Technology-for-the-Poorest-Billion/2026-Ideabatic/interim/Ideabatic 2nd presentation.pdf

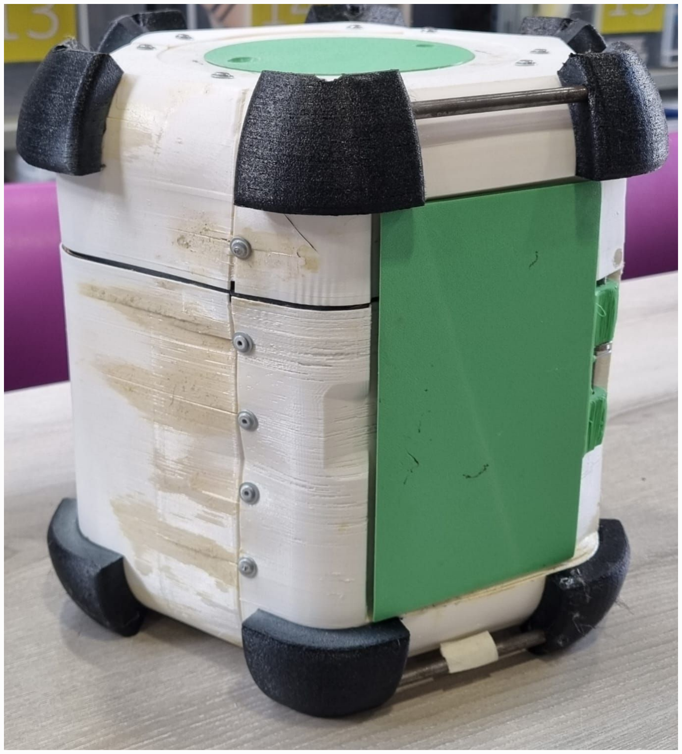
[picture p62: figure]

# IDEABATIC

# SMILE GO Project

# Uniform Cooling Solutions

### Interim Presentation by Karen, Kerry, and Kavita

# Proposal Recap

SMILE GO - Investigating the causes of Asymmetric Cooling & potential ways to reduce it

- In thermal tests the SMILE coolers have shown significant temp difference between top and bottom vaccine carousel chambers
- Issue because vaccines must be stored in small range (2-8°C)
- Design & test cooler inserts
- Investigate impact of convection
- Investigate any other potential causes
- Consider new designs based on our findings

What we will do:

18/05 - 1/06

# Progress So Far

01

# Electronics

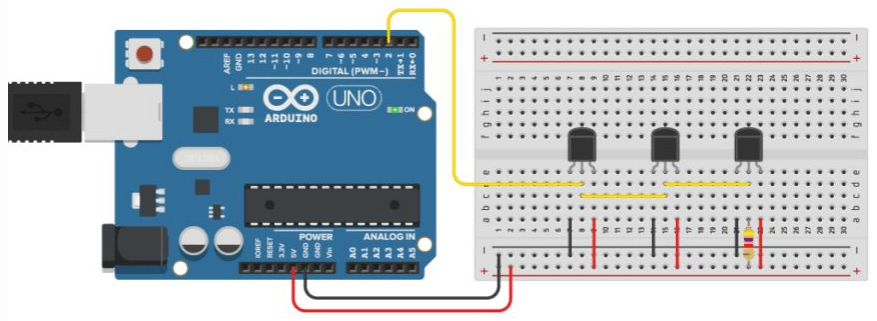
[picture p63: figure]

Supplies | Quantity | Source
DS18B20 | x5 (6) | RS components
breadboard | x1 | CUED
Arduino Uno | x1 | CUED
SD card module | x1 | CUED
4.7k resistor | x1 | CUED
RTC | x1 | RS components

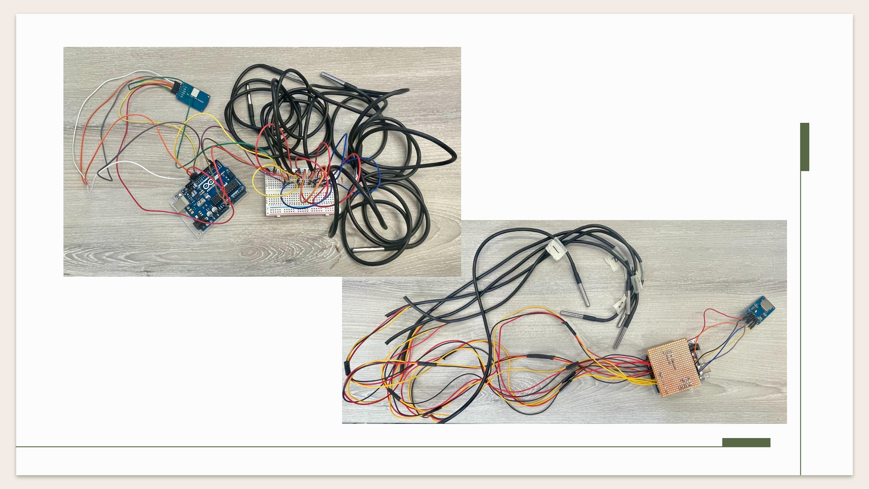
[picture p64: page 5]

# Insert Designs

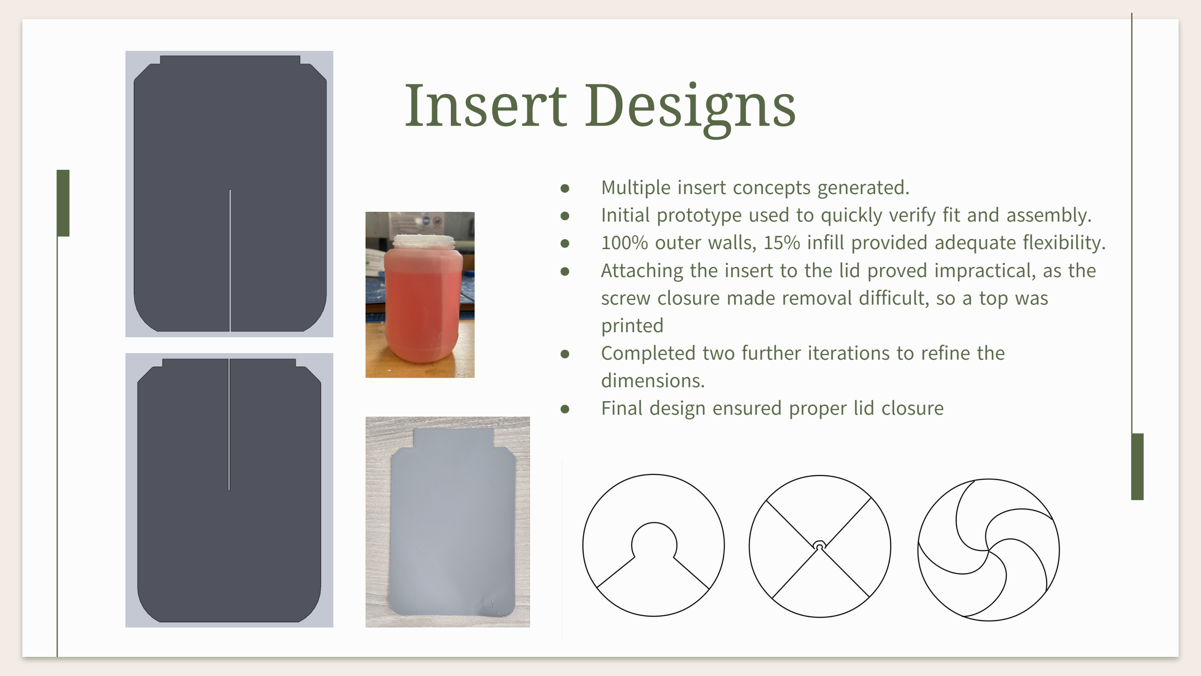
[picture p65: page 6]

- Multiple insert concepts generated.
- Initial prototype used to quickly verify fit and assembly.
- 100% outer walls, 15% infill provided adequate flexibility.
- Attaching the insert to the lid proved impractical, as the screw closure made removal difficult, so a top was printed
- Completed two further iterations to refine the dimensions.
- Final design ensured proper lid closure

# Waterproofing and Freezing

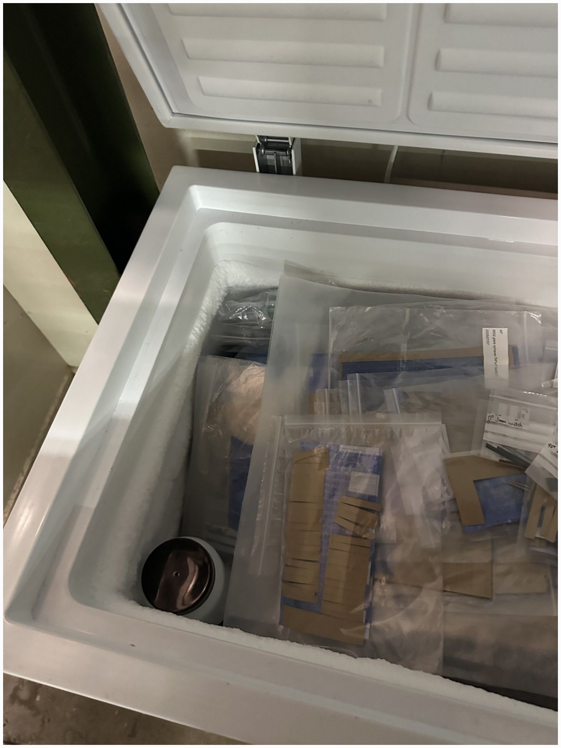
[picture p66: figure]
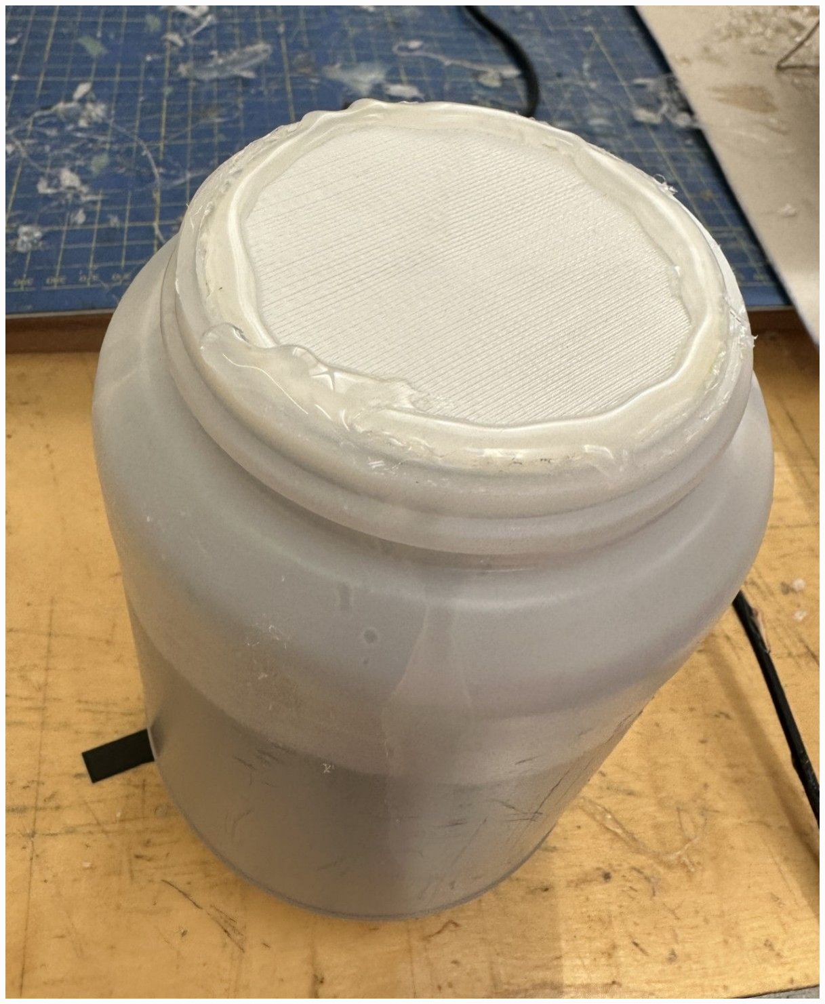
[picture p67: figure]

Hot glue was used to bond the insert into the bottle and form an airtight/watertight seal.

3D print did show some wicking between the extrusion lines using the RS Ideawork printers

The bambu printed lid remained dry

Frozen in the materials lab

# Hot Gluing

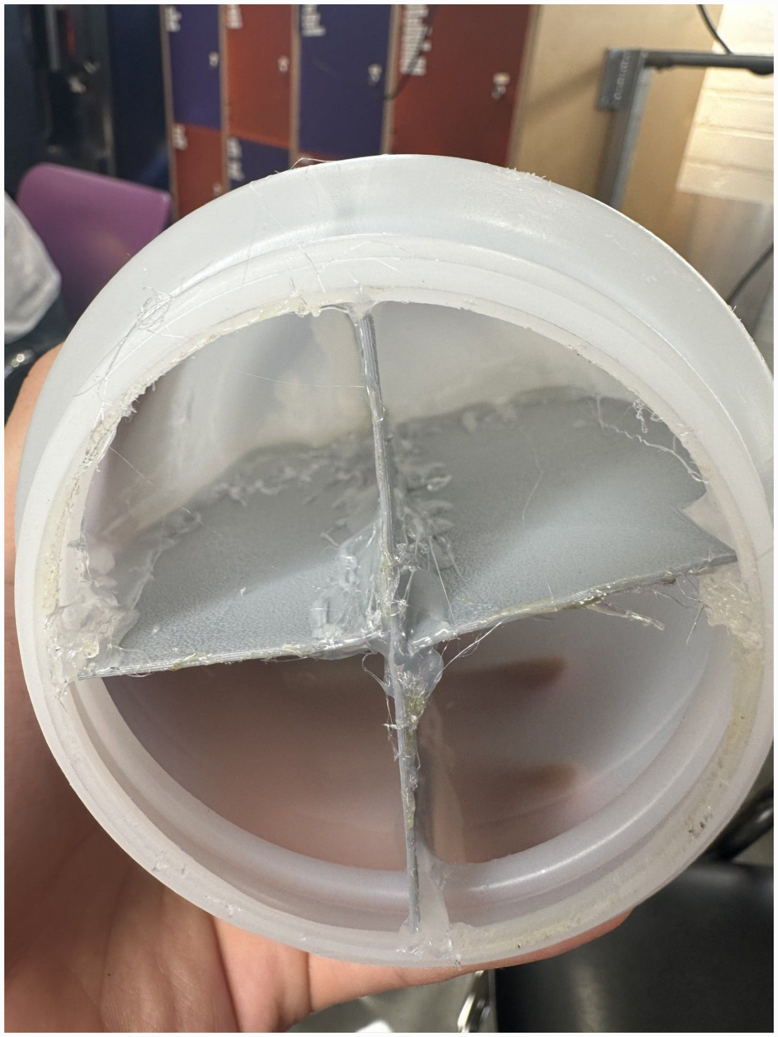
[picture p68: figure]

Extremely sticky. Practice gluing was performed on a sample that was not used for a test to learn more about the process.

The best method seemed to be letting gravity pull the glue down into the interfaces, rather than using sticks or tools to guide the glue.

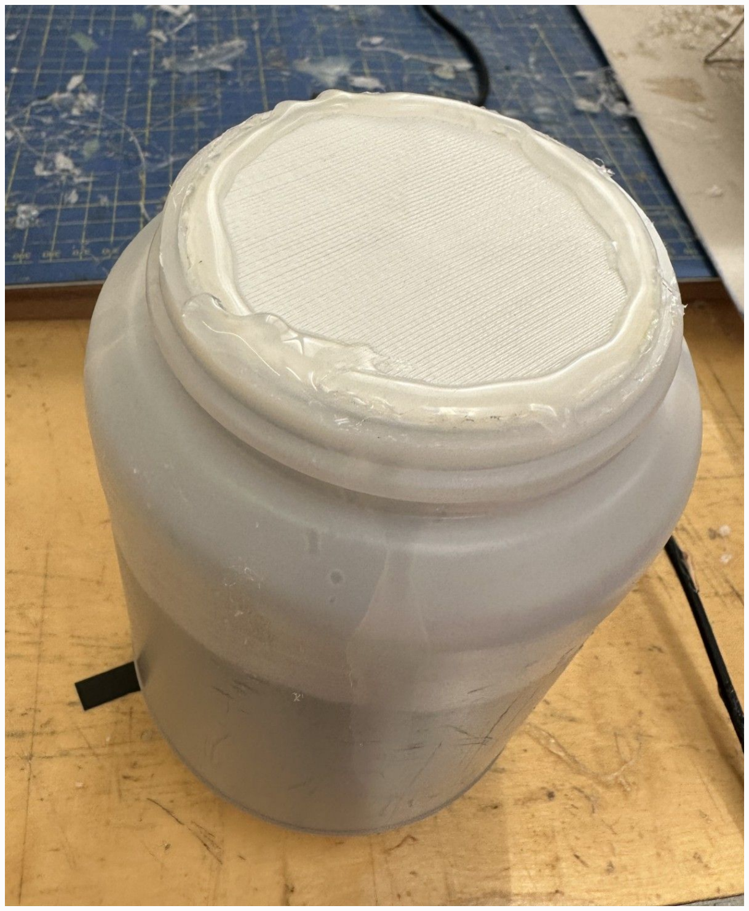
[picture p69: figure]

Further issues include navigating the threaded section of the bottleneck, and gluing the final cap on the bottle.

No “touch-ups” can be made to the lid seal after it is on. This is a very important step in the sealing process.

Water must be added prior to lid gluing.

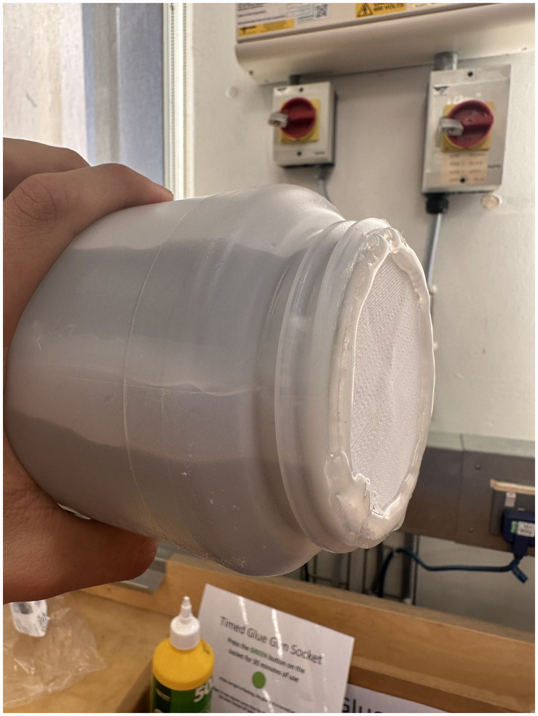
[picture p70: figure]

The seal is airtight and watertight.

Several intermittent testing stages were performed during the gluing process - check and re-apply glue to leaking spots.

A freeze-thaw cycle was performed before testing - the structural integrity of the inserts and seal remained sound.

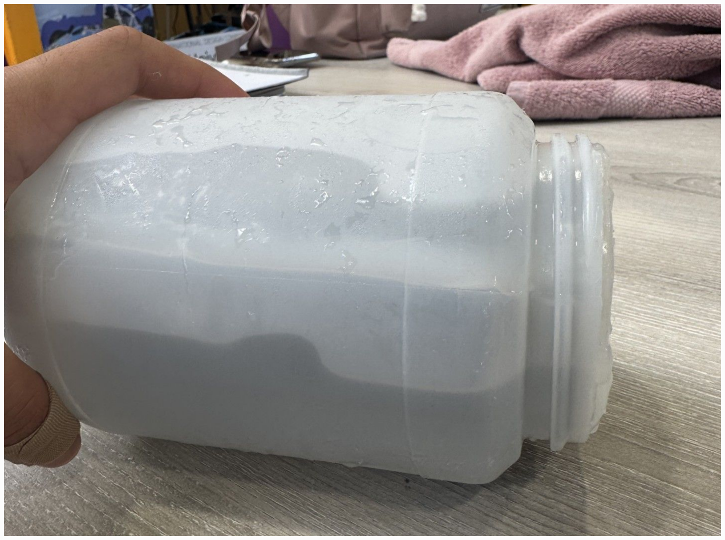
[picture p71: figure]

Updates Hot Glue Expenditure: ~£5

# Gluing Effectiveness

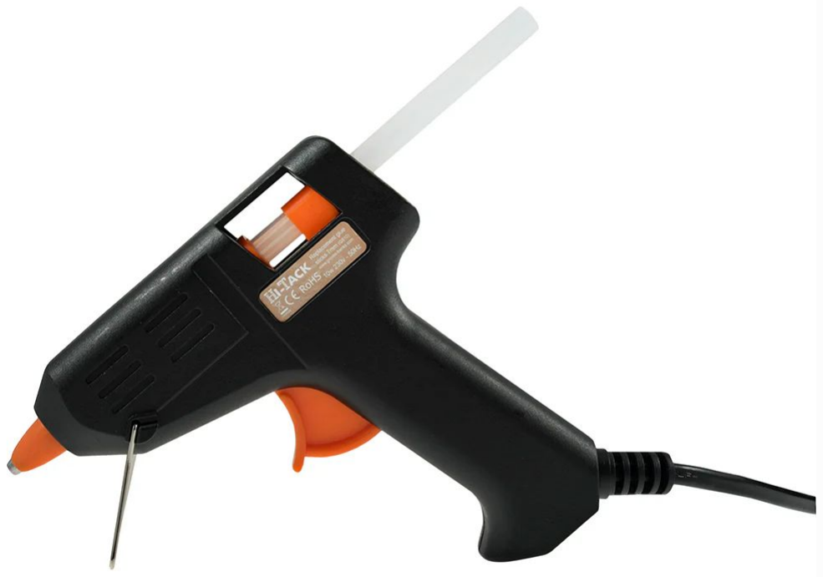
[picture p72: figure]

Removal of the insert and hot glue seal in the bottle can be done with minimal damage to the bottle.

A check was performed prior to insert addition to assess hot glue adhesion properties to the bottle.

Hot glue delaminates from the HDPE bottle with enough force.

Inserts are damaged in the process, so once they are removed, they cannot be reused.

# Hot Glue and Insert Removal

- Prototype Material Selection
- PLA chosen for rapid, low-cost manufacture
- Hot glue used to create temporary airtight seals for testing.
- Key Issues Identified
- Water permeation through the printed structure due to print porosity.
- PLA experiences hydrolytic degradation over time
- Potential degradation of PLA and adhesive seals during freeze-thaw cycling.
- Design Improvements
- Higher-quality Bambu printing reduced porosity and improved consistency.

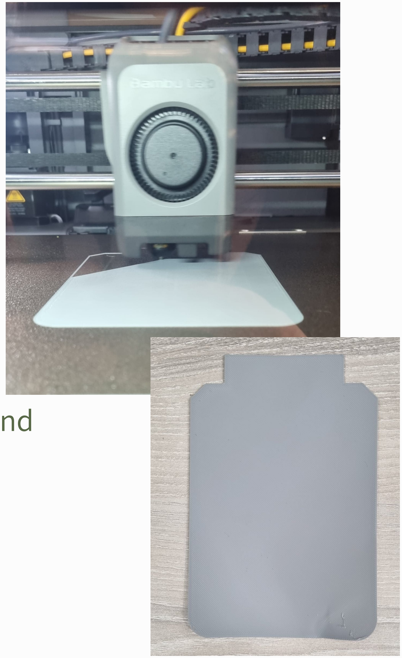
[picture p73: figure]

- PETG identified as a more suitable material due to improved water resistance and takes up less moisture
- Future Manufacturing
- Current solution suitable for prototyping only.
- Integrated blow-moulded chambers.
- Silicon sealant remains flexible, epoxy coating

# Material Research for Insert Design

# Experimental set-up

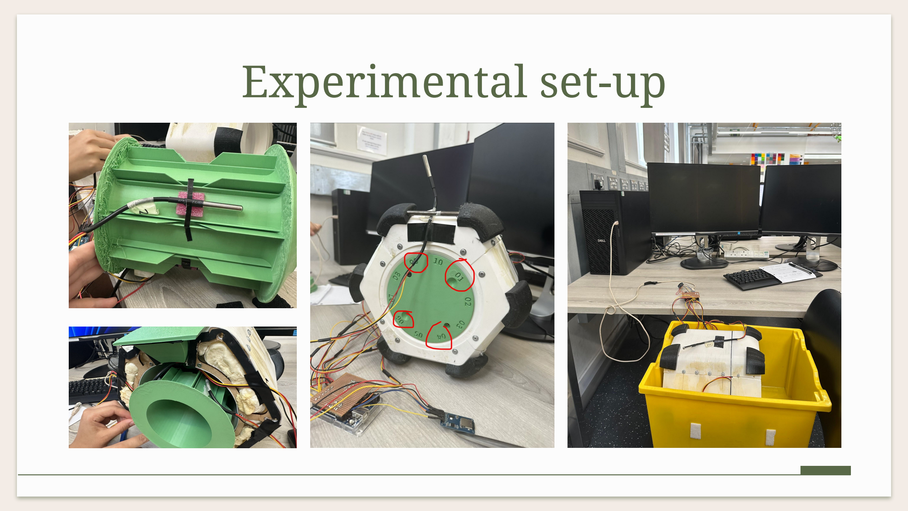
[picture p74: page 12]

01 Control test - 24 hour control test with the current set-up and the door on top (no inserts).

# Experimental testing

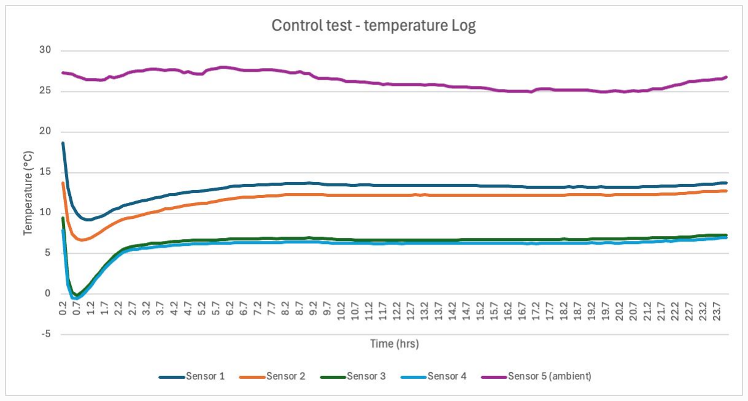
[picture p75: figure]

Results: Initial difference in temperature (1st measurement 5mins in). Temperature drops significantly then rises back to a stable temperature after 5-6 hours

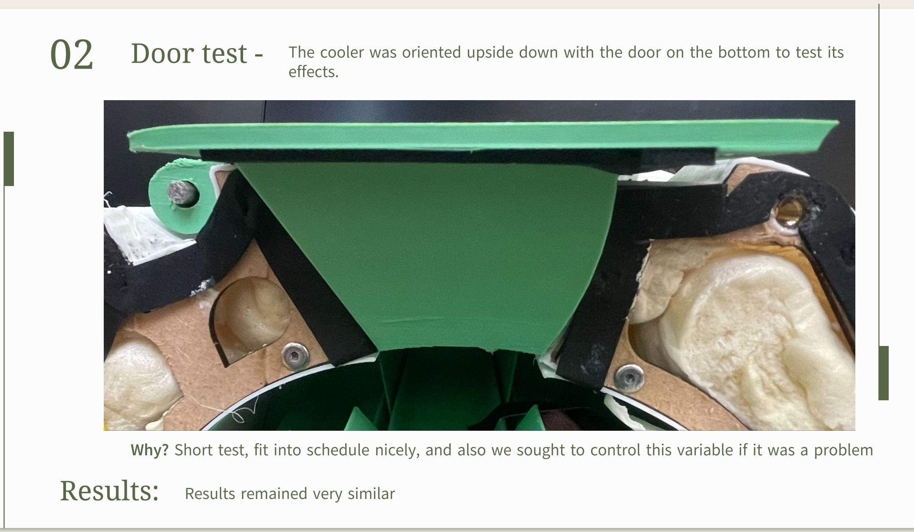
[picture p76: figure]
Door test -; Results:; Results remained very similar; effects.

Why? Short test, fit into schedule nicely, and also we sought to control this variable if it was a problem

The cooler was oriented upside down with the door on the bottom to test its

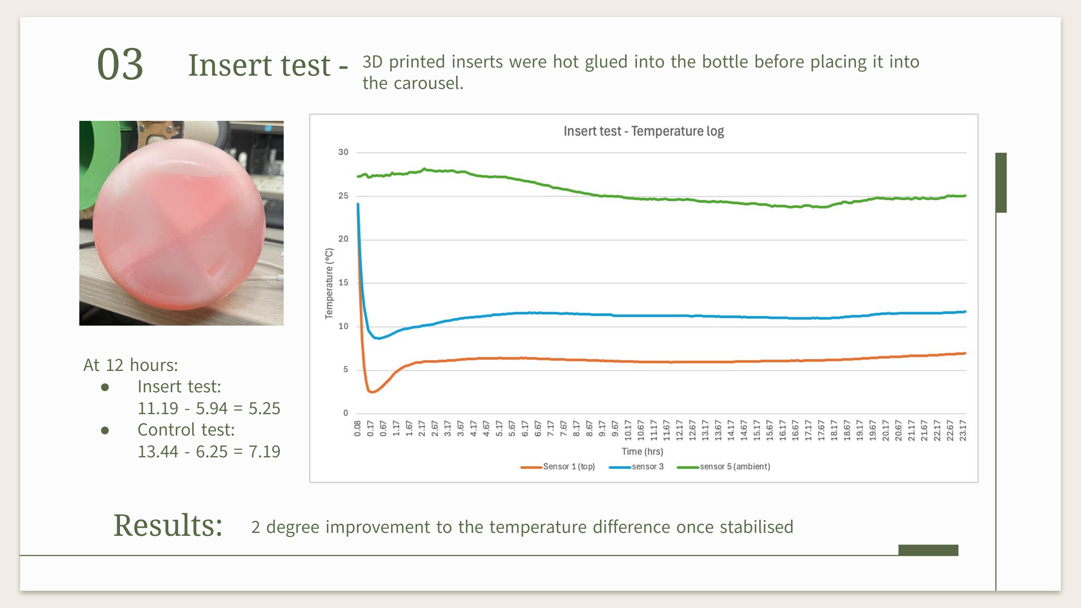
[picture p77: page 15]

03 | 3D printed inserts were hot glued into the bottle before placing it into
the carousel. Insert test -

Results: 2 degree improvement to the temperature difference once stabilised

At 12 hours:
- Insert test:
11.19 - 5.94 = 5.25
- Control test:
13.44 - 6.25 = 7.19

04

## Top thermal contact test -

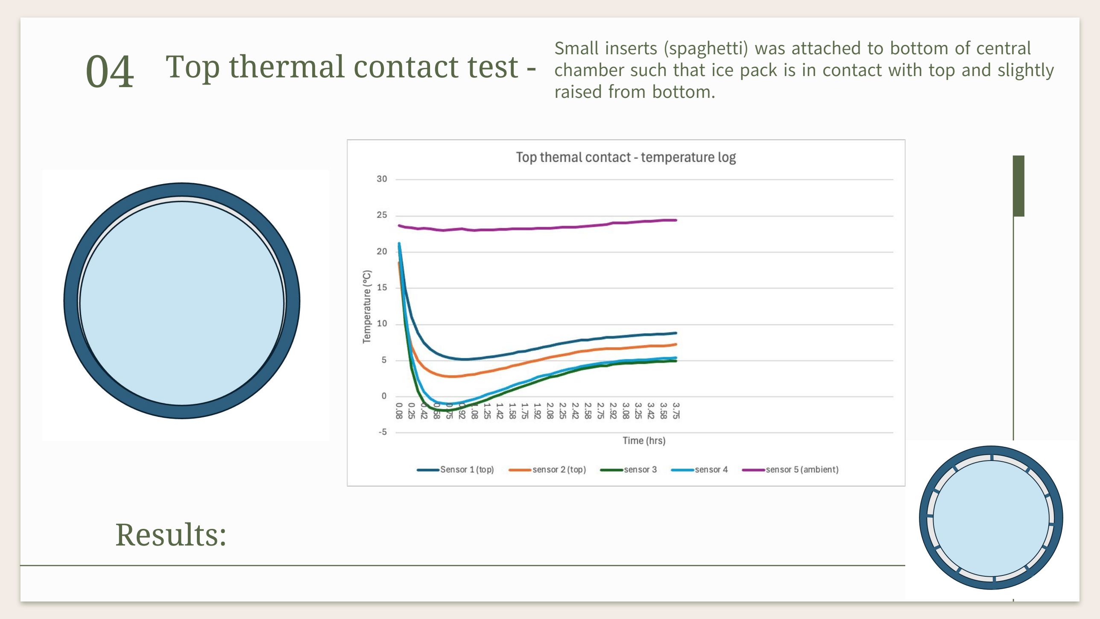
[picture p78: page 16]

Small inserts (spaghetti) was attached to bottom of central chamber such that ice pack is in contact with top and slightly raised from bottom.

## Results:

# Convection Research

- Research into convection-based experimental methods and setup designs
- Convection Resistance Design - radial planes in vaccine carousel
- Forced Convection - fan-induced convection and mixing

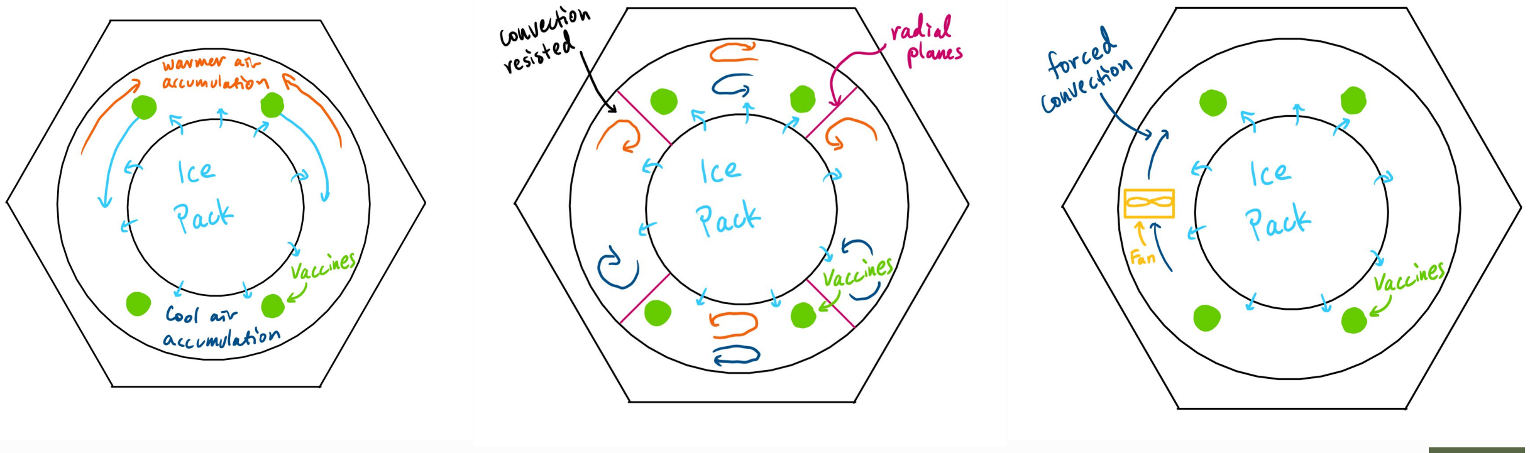
[picture p79: figure]

# Convection Prototype

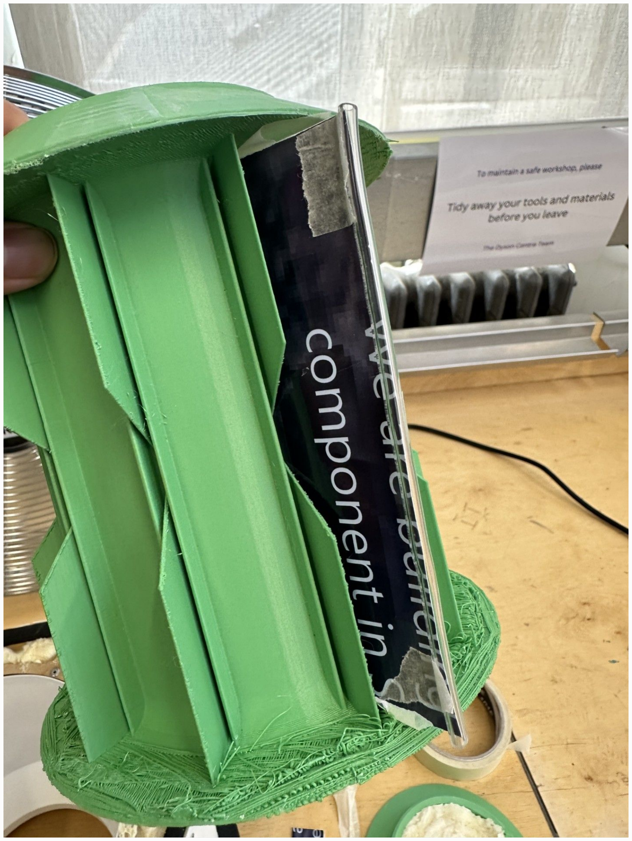
[picture p80: figure]
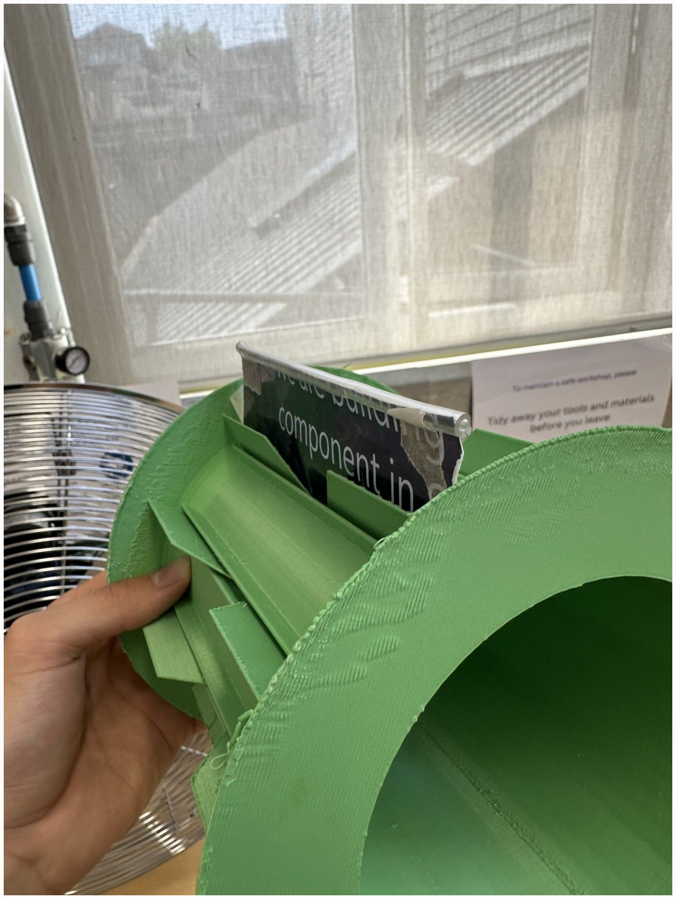
[picture p81: figure]

A brief model of the experimental setup for the convection resisting design was constructed.

- Assessment of how difficult it may be to get a decent seal within the vaccine chamber.
- Conclusion: very difficult, especially with assembly considerations.

However, it is still worth performing the test to assess the effectiveness of a simple carousel design which may end up mitigating the non-uniform cooling issue.

We want to see, if convection is the issue, if a simple redesign of the carousel can effectively even out the cooling.

# Documentation

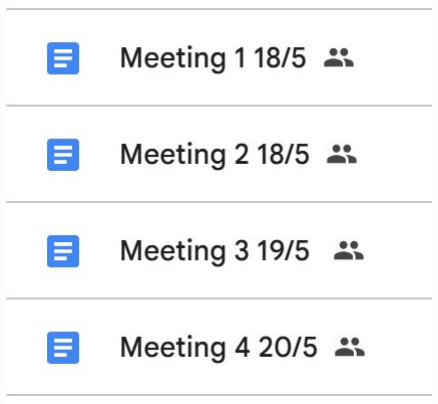
[picture p82: figure]

- Document of images taken throughout the project -important to keep track of specific design choices and for use in presentations or report.
- Meeting summaries consistently taken to keep track of ideas and possible changes to the project.

# Further Issues

02

Issue Encountered | Mitigation
Delays in sensor procurement affected the original testing schedule | Adapted the schedule and prioritised alternative tasks
Only one cooler bottle was available for testing and the current bottle is sold out | Carefully planned testing schedules to maximise bottle usage
Communication over text messages was sometimes ineffective in conveying ideas | Consistent and increased the frequency of in-person meetings
Early-stage challenges with file organisation and access across the team | Adopted Google Drive for centralised file sharing
Uncertain if the test will fail overnight or the computer has to be turned off | SD card stores any data till that point. We have contingency plans in case we can’t access the computer

# Personal and Technical development

03

# Kerry

- Attention to detail - The hot gluing process requires patience and a willingness to redo sections to get a sufficient seal.
- Importance of iteration and practice
- Communication with technicians and experts

# Kavita

- Code and arduino debugging (COM port issues)
- Soldering skills
- Time management & adaptability

# Karen

- Learning practical constraints of 3D printing (porosity, print settings, material selection)
- Iterative designing
- Time management

# Project timeline development

04

# Updated Gantt Chart

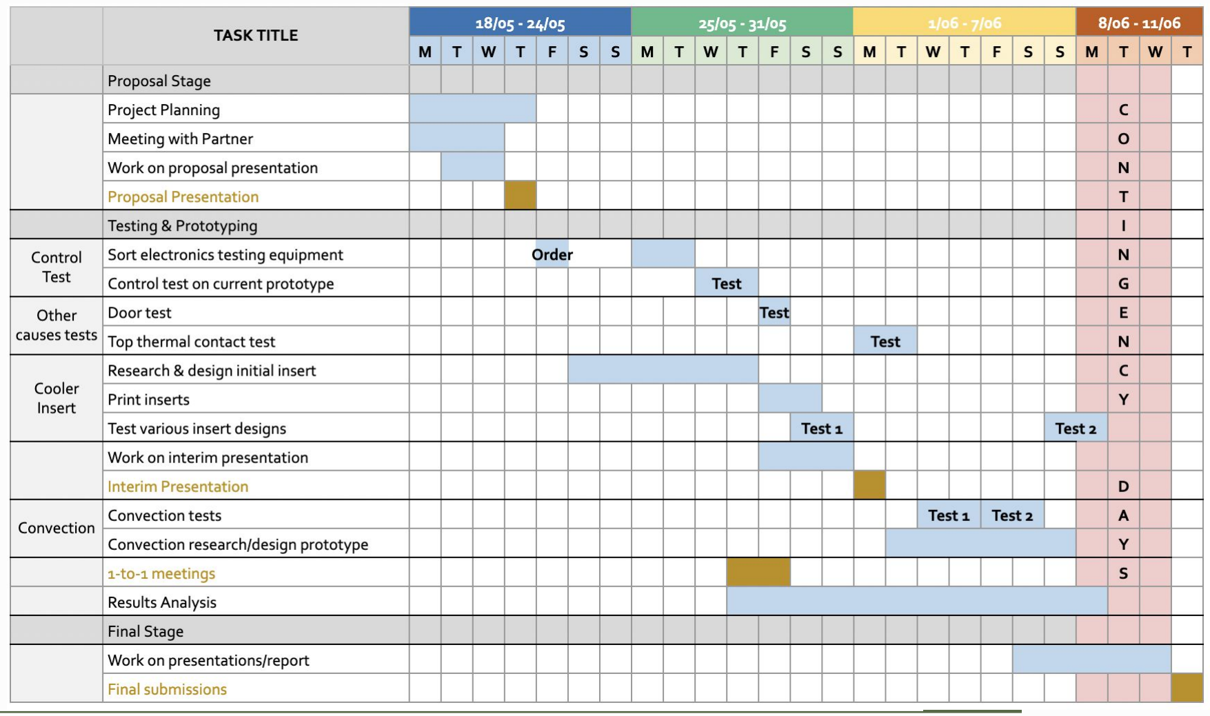
[picture p83: figure]

### Further Testing

# Future plans

- Convection test - fan (contacted Kevin for purchasing), radial planes.
- Investigate effect of contact of the ice pack with only the lower section of the carousel on non-uniform cooling.

### Analyse Results

- Compile the test data to analyse any significant changes.

### Design Changes

- Provide possible solutions to any identified causes of non-uniform cooling.

### Key Findings

- There is a large initial temperature difference occurs during the first 10 minutes.
- Door leakage largely ruled out
- Ice segmentation showed some promise of improving cooling uniformity.
- No definitive root cause identified. Further investigation required.
- Better Insulation required in the SMILE Go to keep vaccines in correct range

# Thank you for listening

### Any questions?
