Technology-for-the-Poorest-Billion/2026-Ideabatic/final/Technical Files/Research and Documentation/Image Documentation/Documentation_Images.pdf

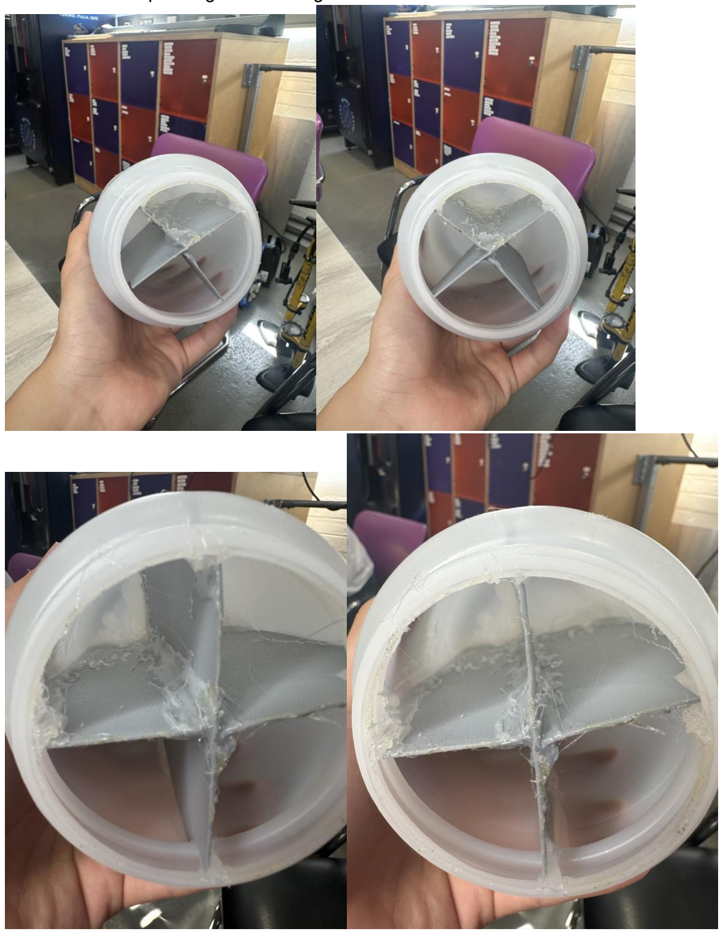
[picture p104: figure]

First insert water proofing and freezing:

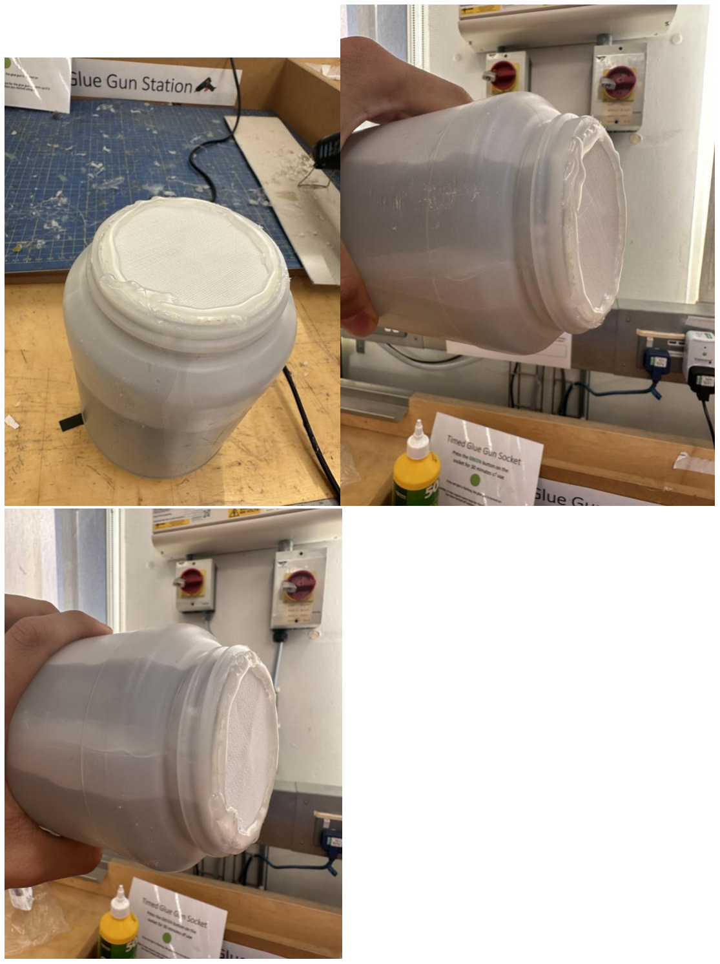
[picture p105: figure]

Once frozen and thawed to a large degree:

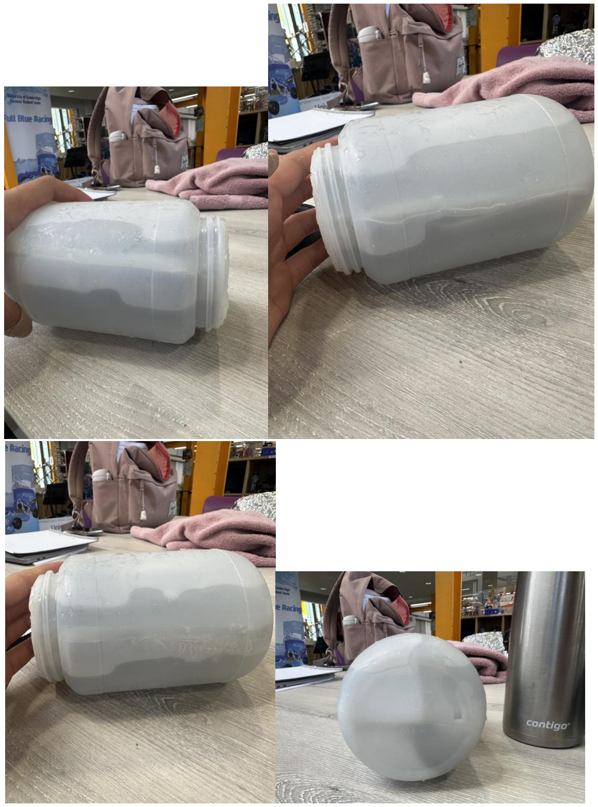
[picture p106: figure]

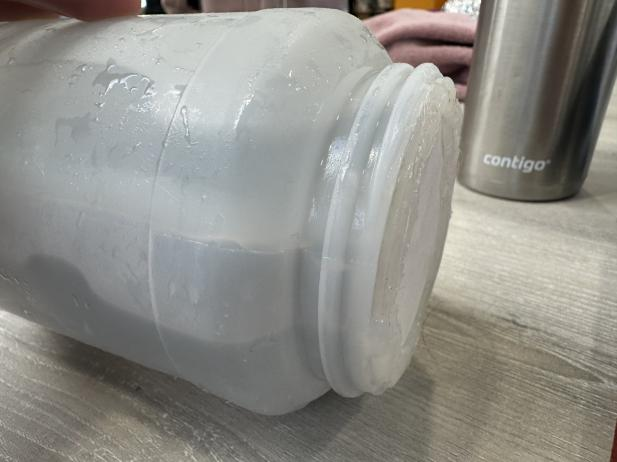
[picture p107: figure]

3D print of the insert initially:

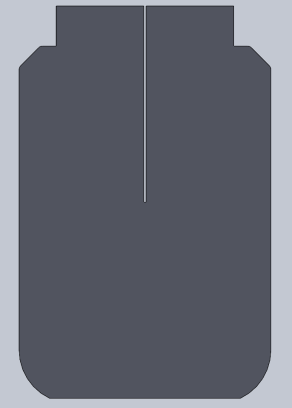
[picture p108: figure]
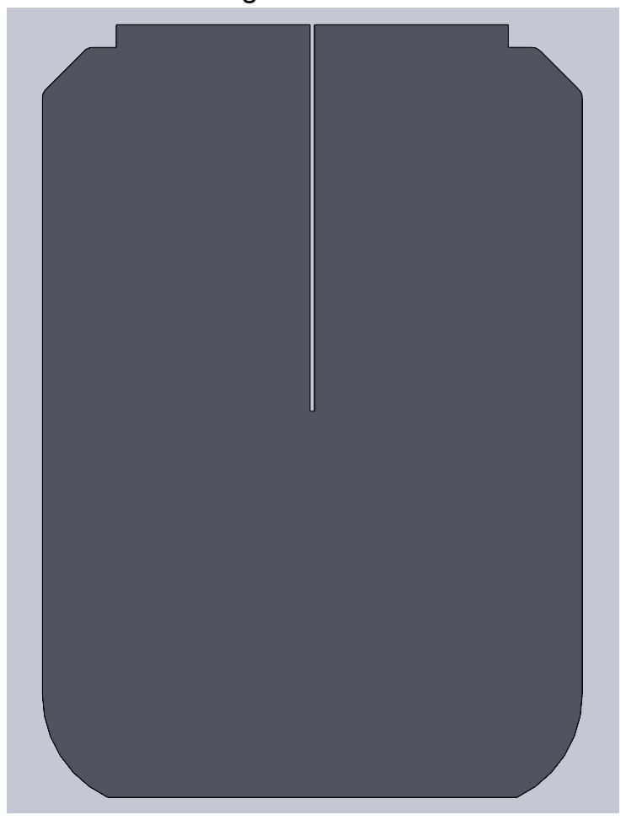
[picture p109: figure]

Newer insert design:

Convection FIrst test with tape and rubber seal:

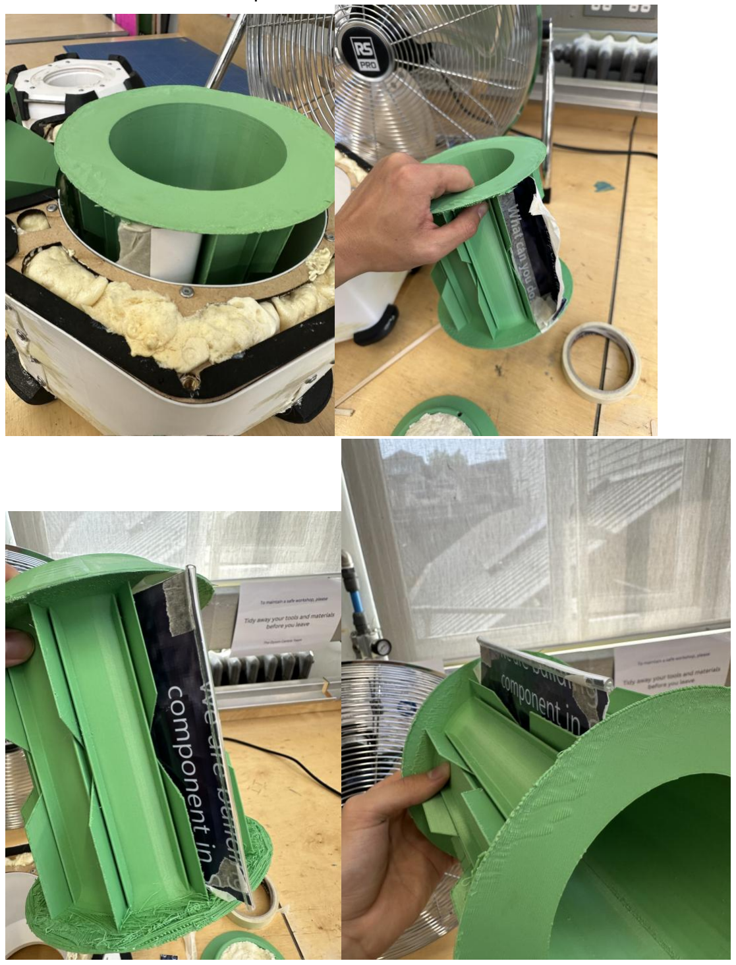
[picture p110: figure]

Freezer in the Materials Lab:

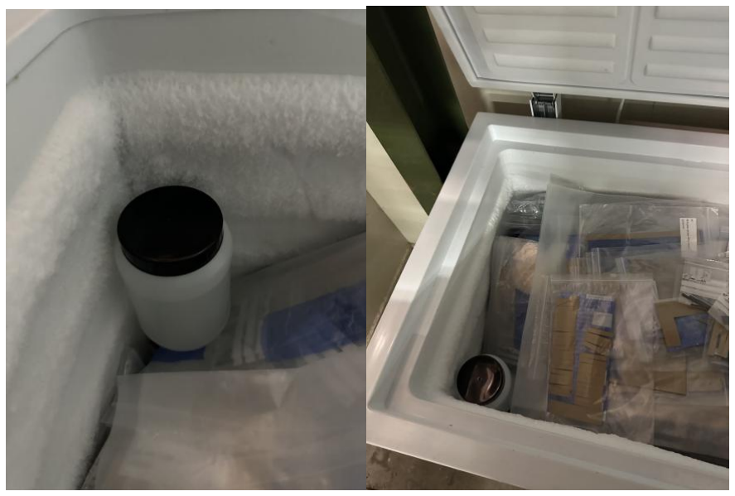
[picture p111: figure]

Frozen control:

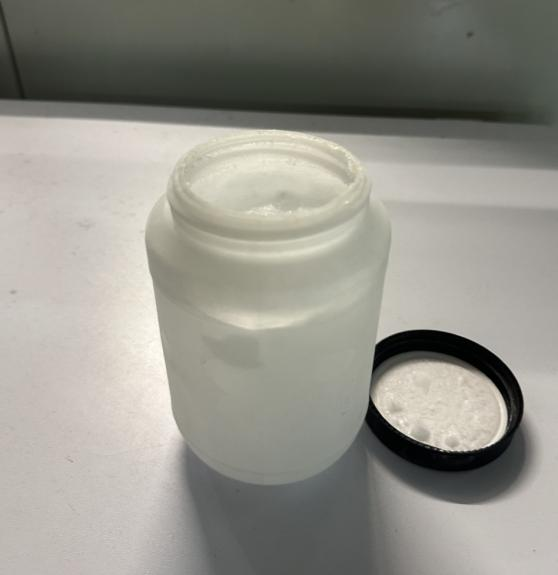
[picture p112: figure]

Initial breadboarded circuit:

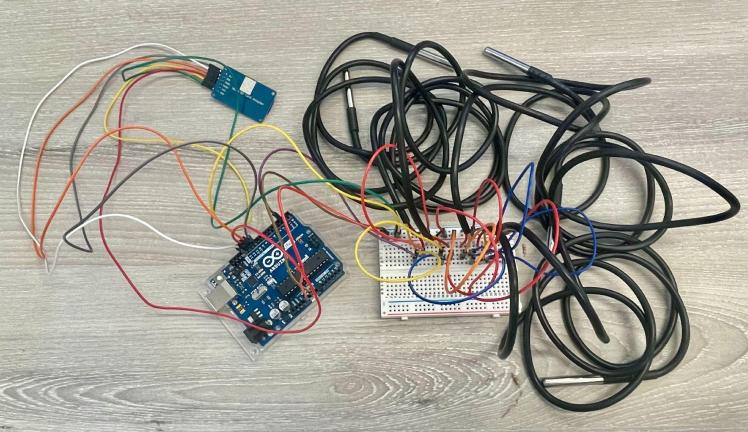
[picture p113: figure]

Soldered circuit:

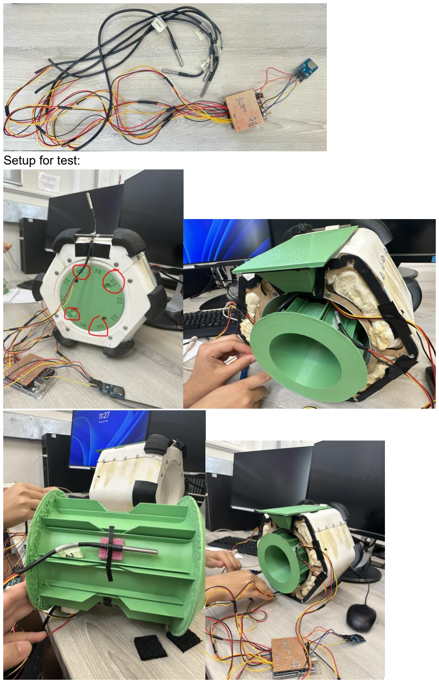
[picture p114: page 7]

Setup for test:

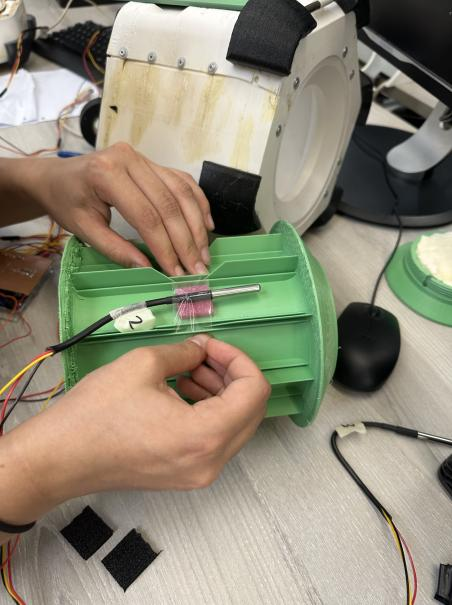
[picture p115: figure]

Test with door down:

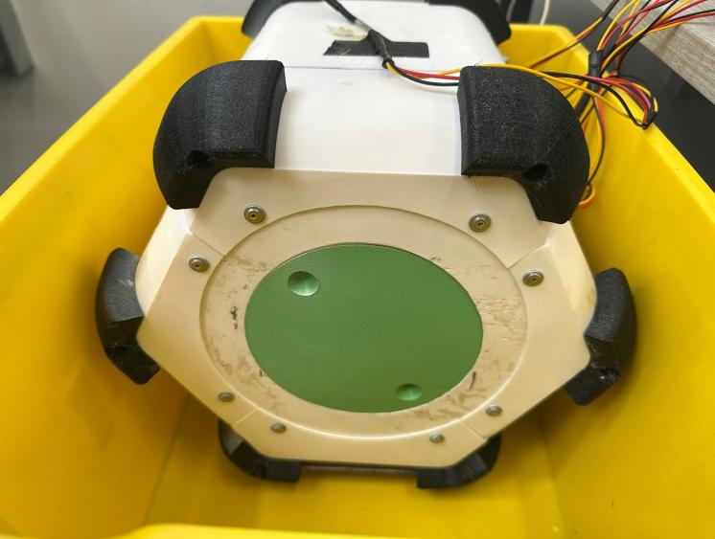
[picture p116: figure]

Experimental setup:

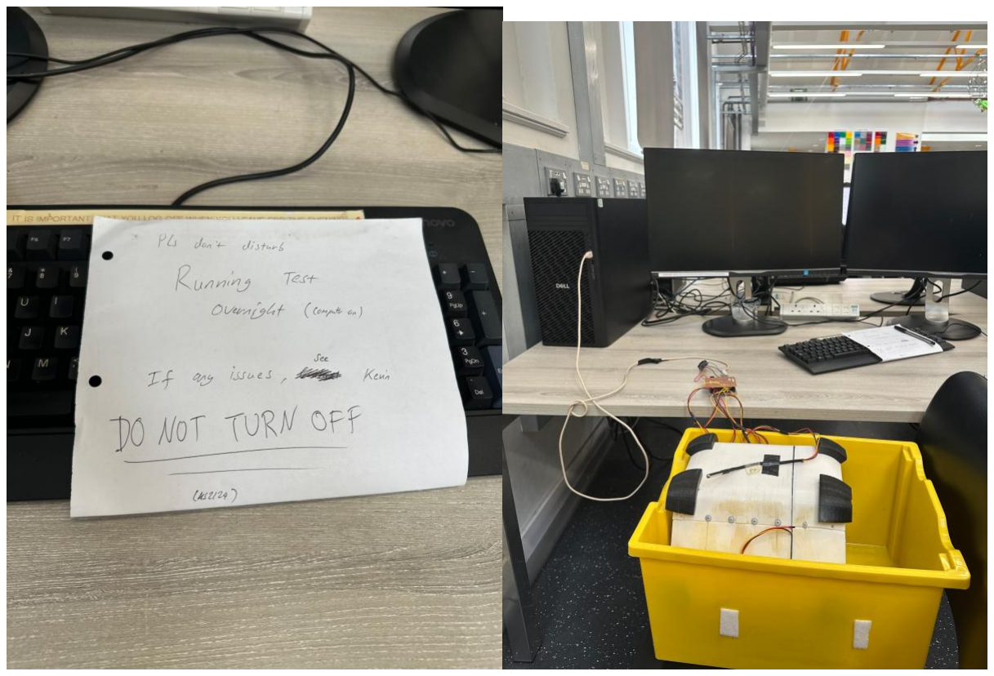
[picture p117: figure]

first insert test, gluing and bottle:

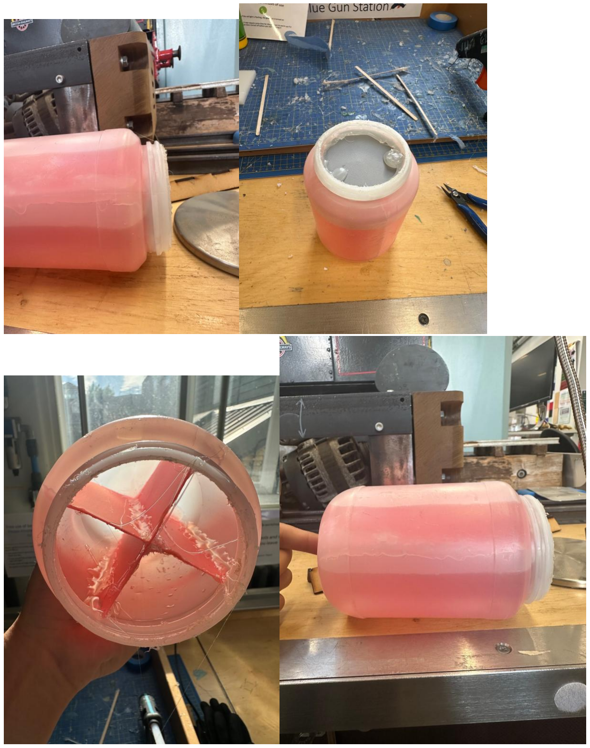
[picture p118: figure]
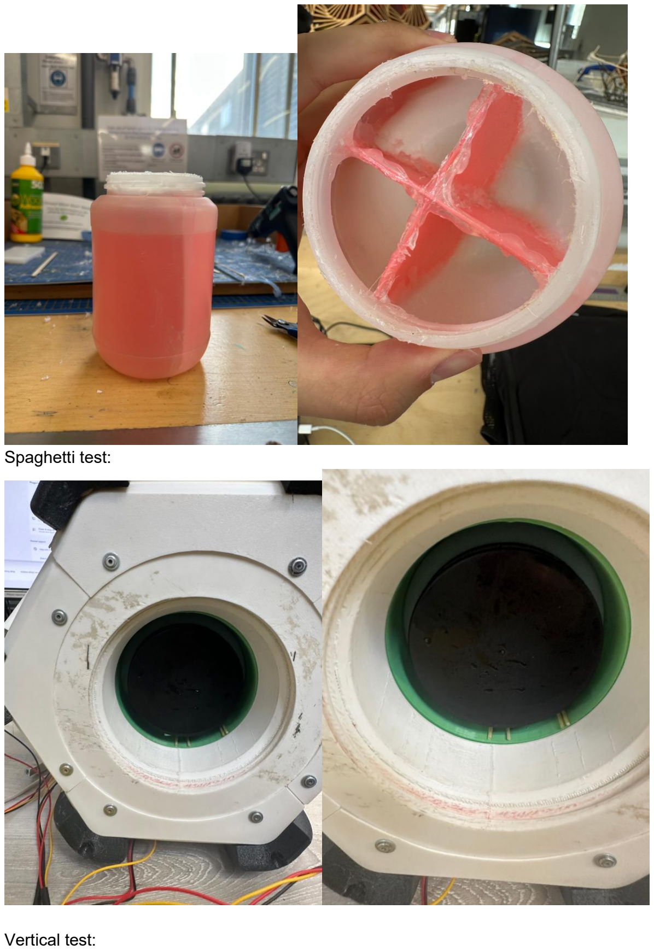
[picture p119: page 11]

Spaghetti test:

Vertical test:

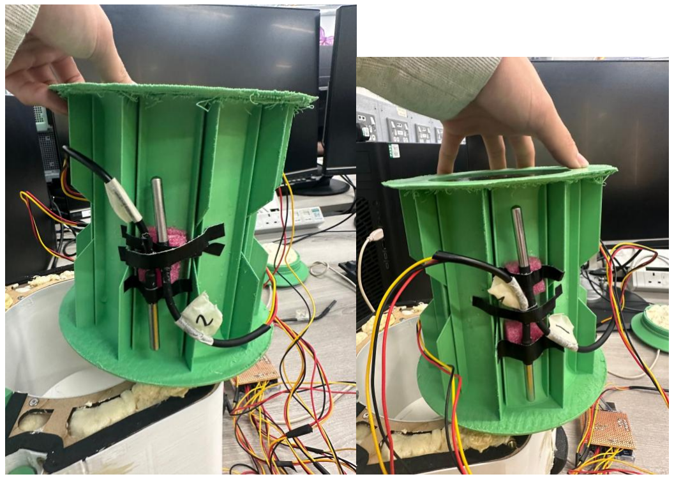
[picture p120: figure]

Radial Planes:

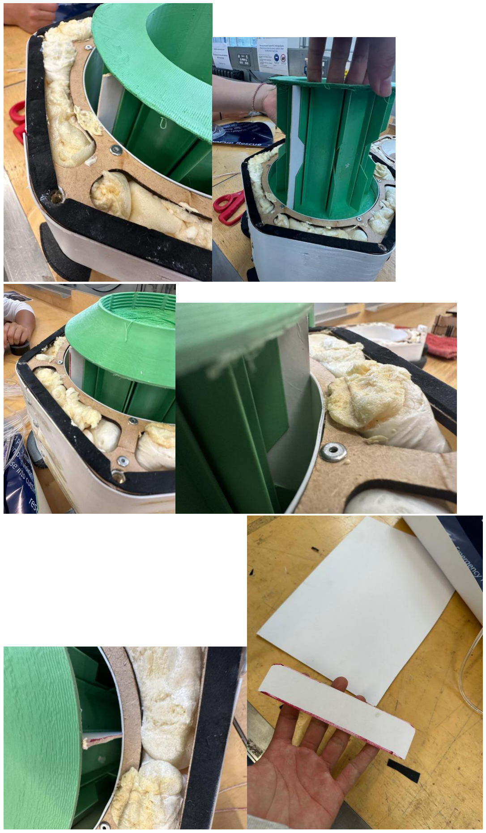
[picture p121: figure]

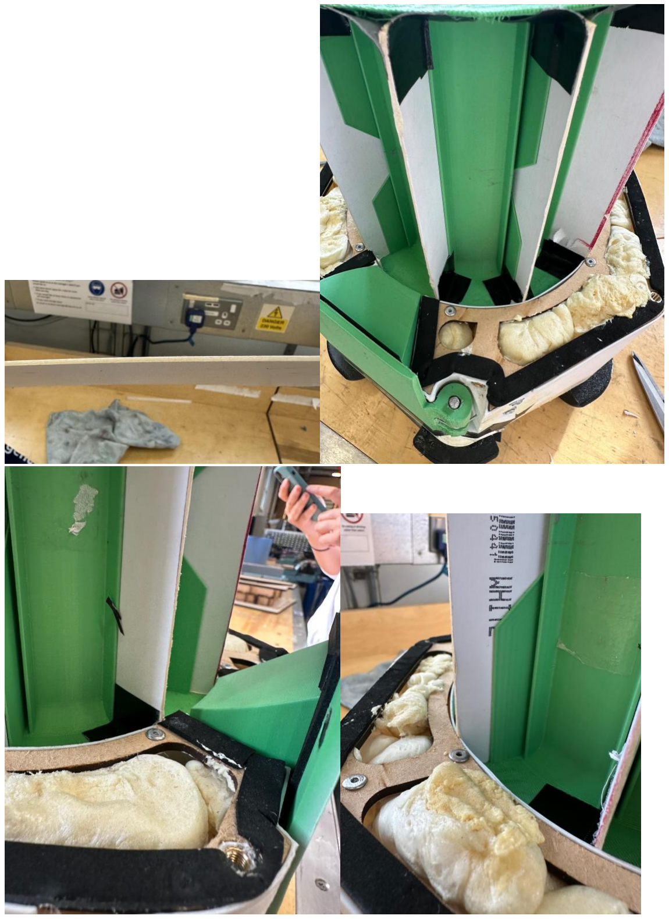
[picture p122: figure]

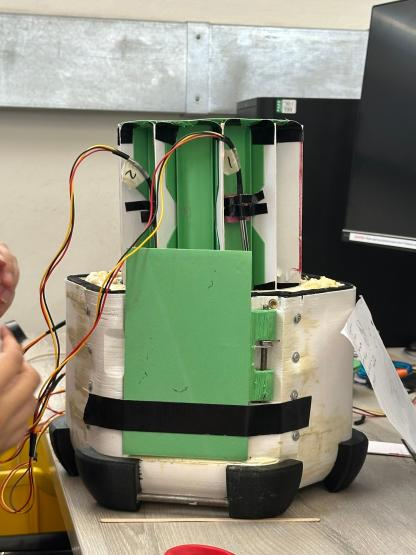
[picture p123: figure]

Radial planes quality AFTER test completed:

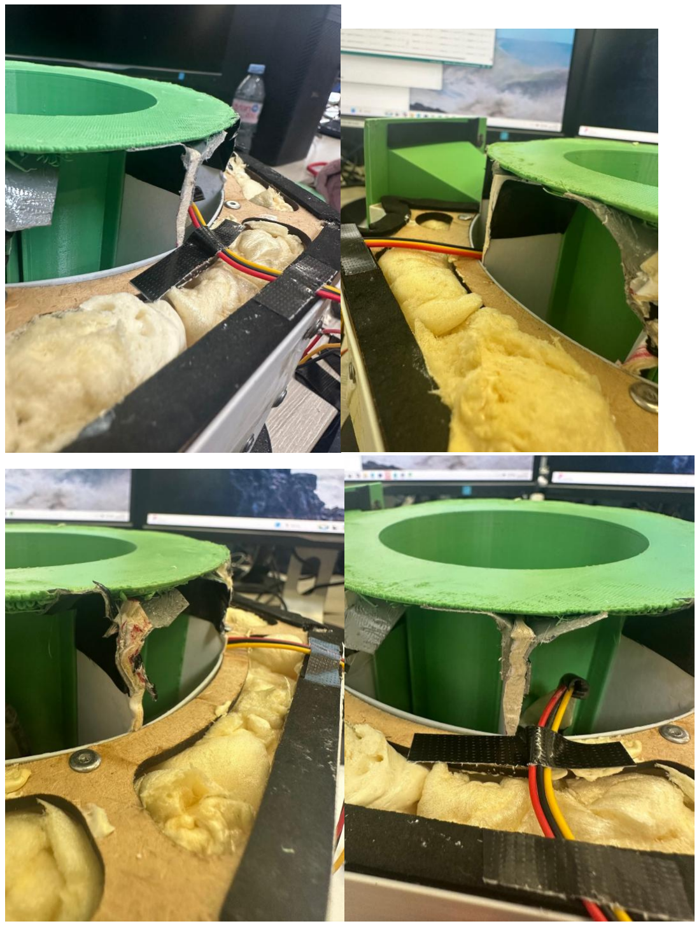
[picture p124: figure]

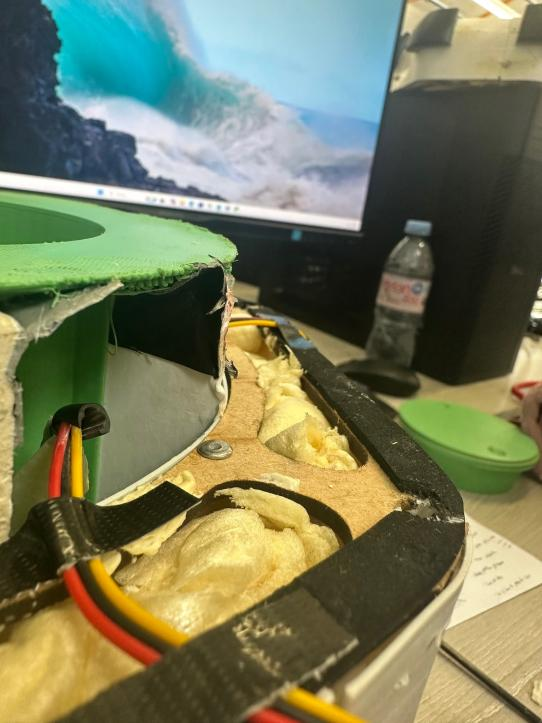
[picture p125: figure]

Water after slight thaw:

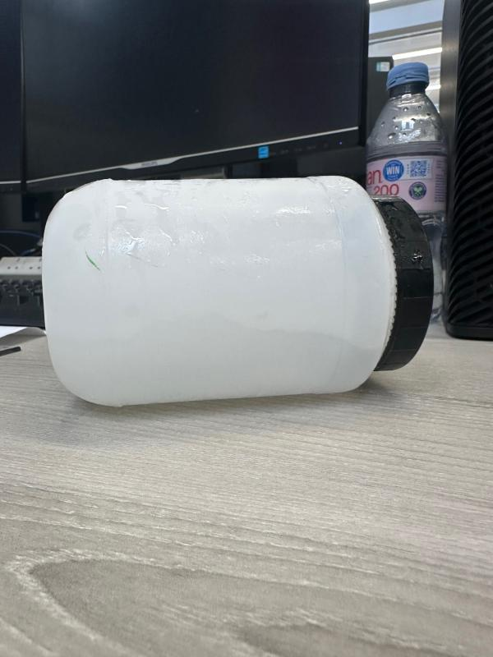
[picture p126: figure]

Radial Plane Validity test with planes:

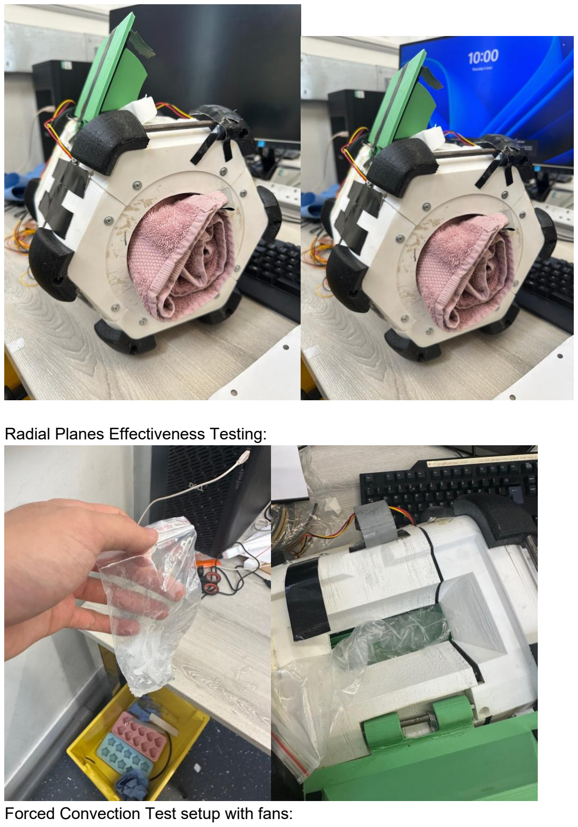
[picture p127: page 18]

Radial Planes Effectiveness Testing:

Forced Convection Test setup with fans:

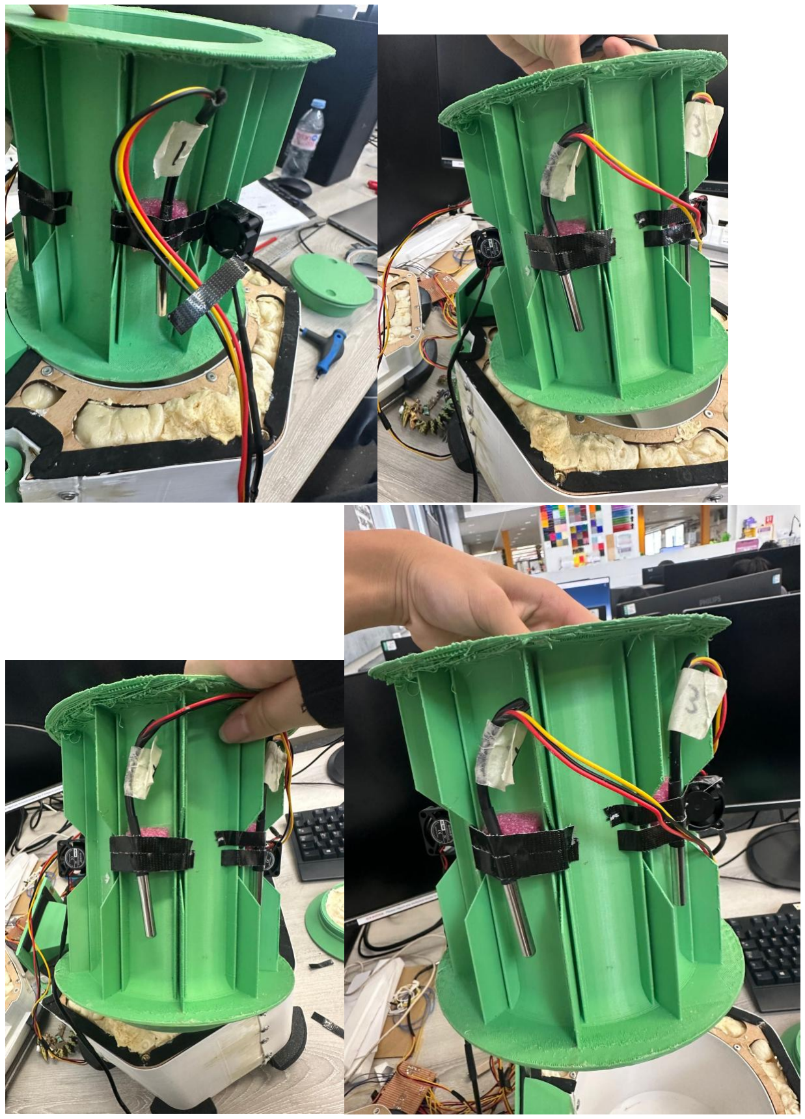
[picture p128: figure]
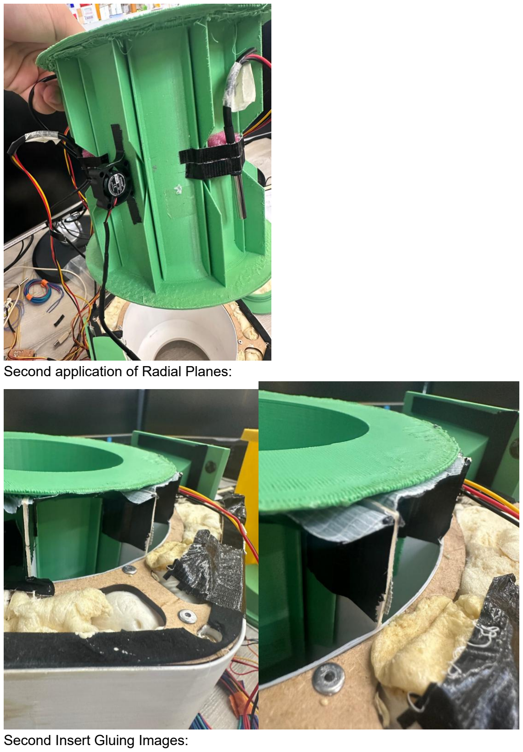
[picture p129: page 20]

Second application of Radial Planes:

Second Insert Gluing Images:

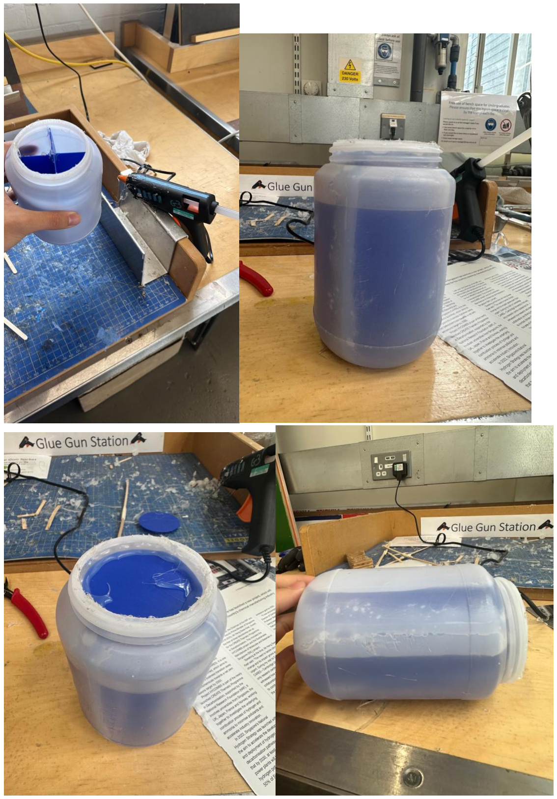
[picture p130: figure]

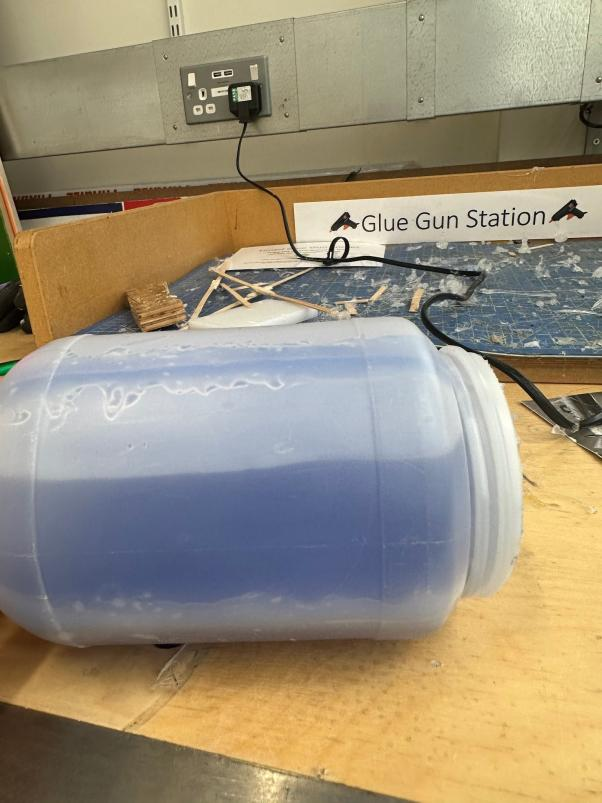
[picture p131: figure]
